WildernessLabs/GNSS_Sensor_Tracker/Design/gnss-tracker-specs.jpg

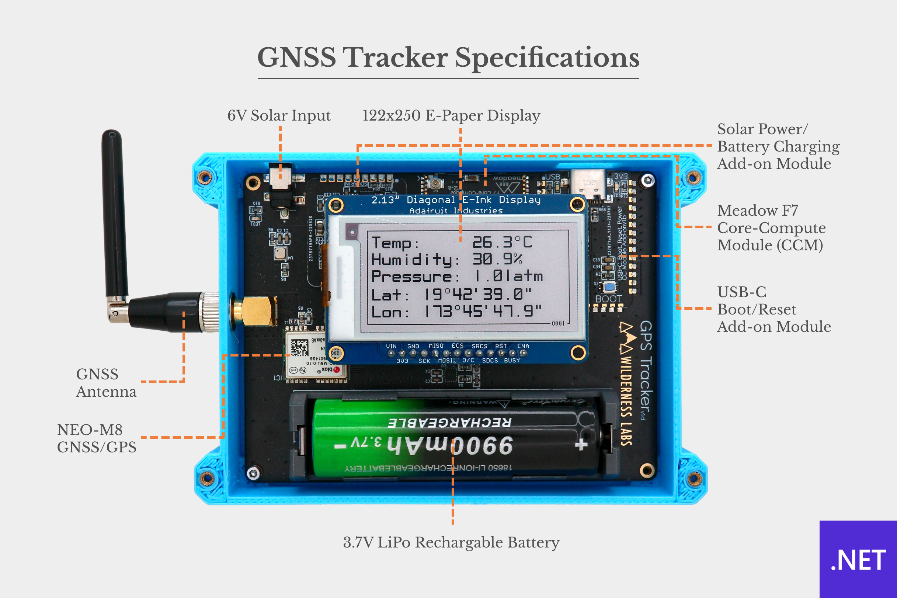
Design/gnss-tracker-specs.jpg
